nikitaignatov/velometa/3d/case-Lid.stl

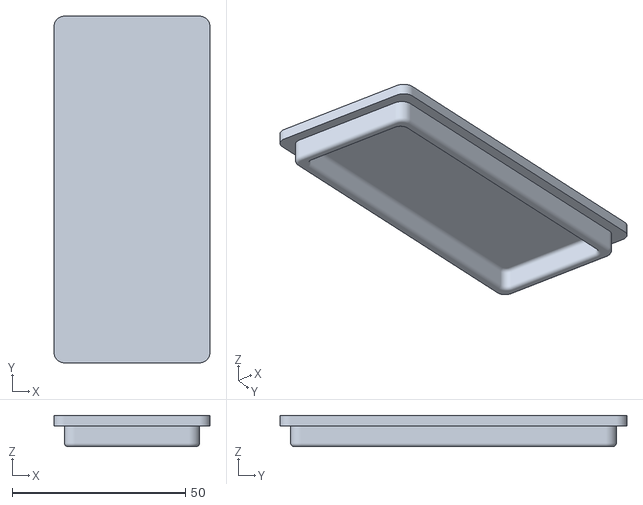
[picture p15: CAD file, 2023-10-30]
3d/case-Lid.stl
45.0 x 100.0 x 9.00
