nikitaignatov/velometa/3d/case-Body.stl

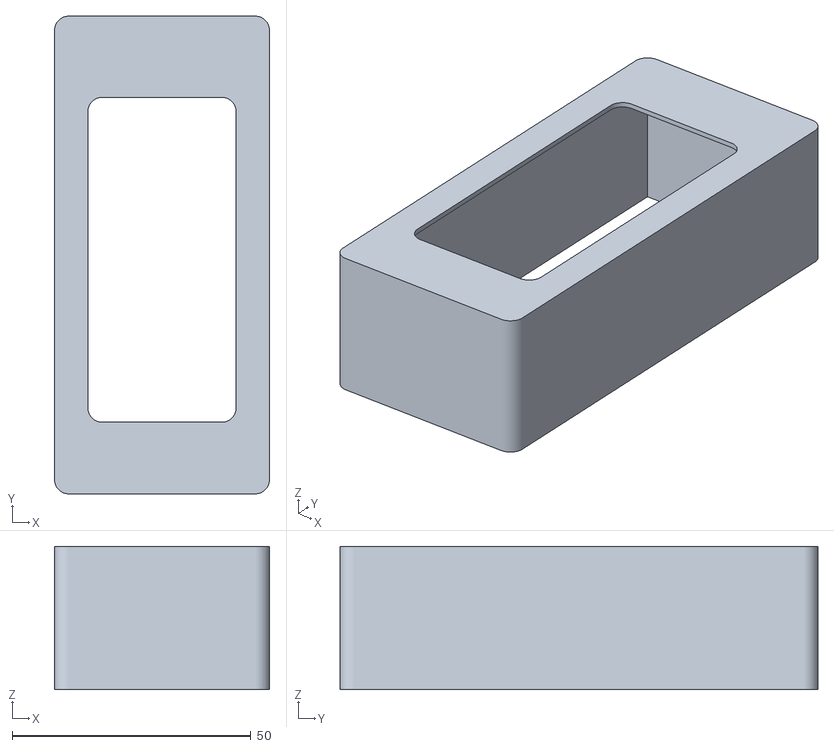
[picture p16: CAD file, 2023-10-29]
3d/case-Body.stl
45.0 x 100.0 x 30.0
